Berraud/M48T08_Clock/IMG_20190323_011705232-01.jpeg

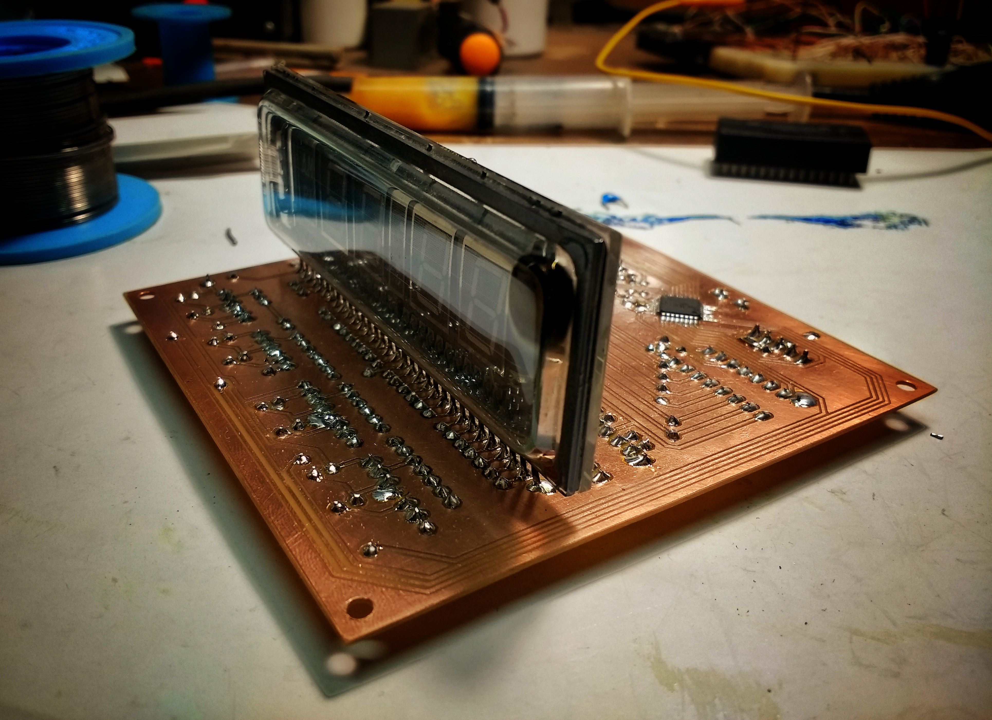
IMG_20190323_011705232-01.jpeg
